qubist/typeO/gallery/prototype-curve.jpeg

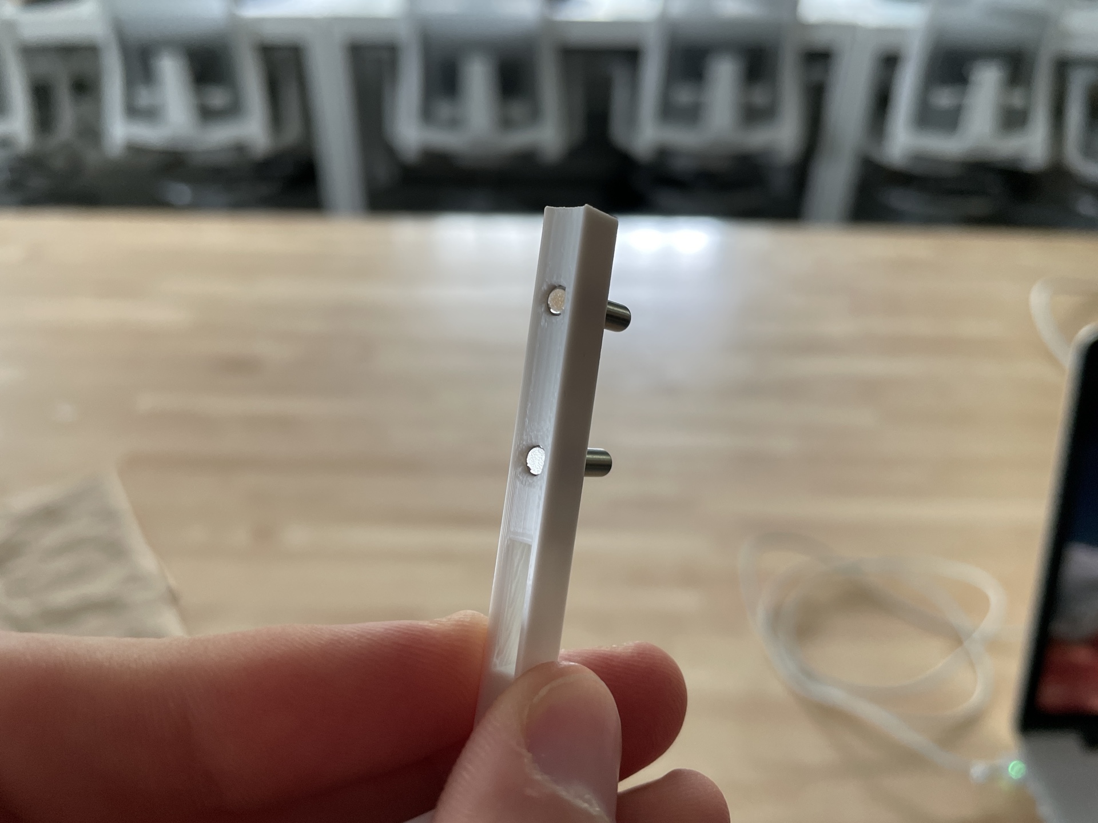
gallery/prototype-curve.jpeg
