qubist/typeO/gallery/prototype-lift.jpeg

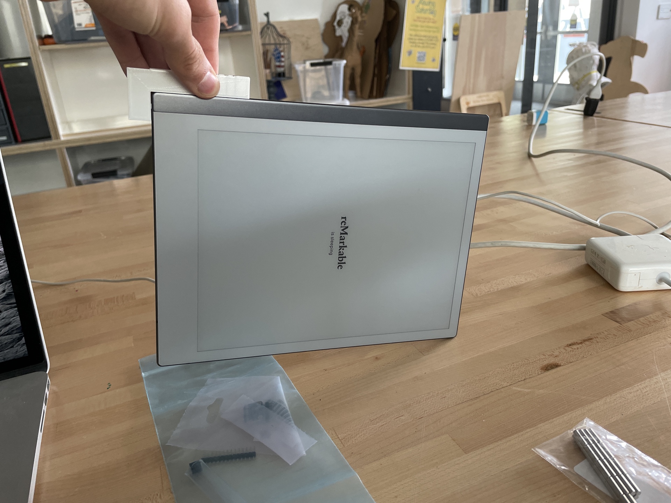
gallery/prototype-lift.jpeg
