qubist/typeO/gallery/magnet-measurements.jpeg

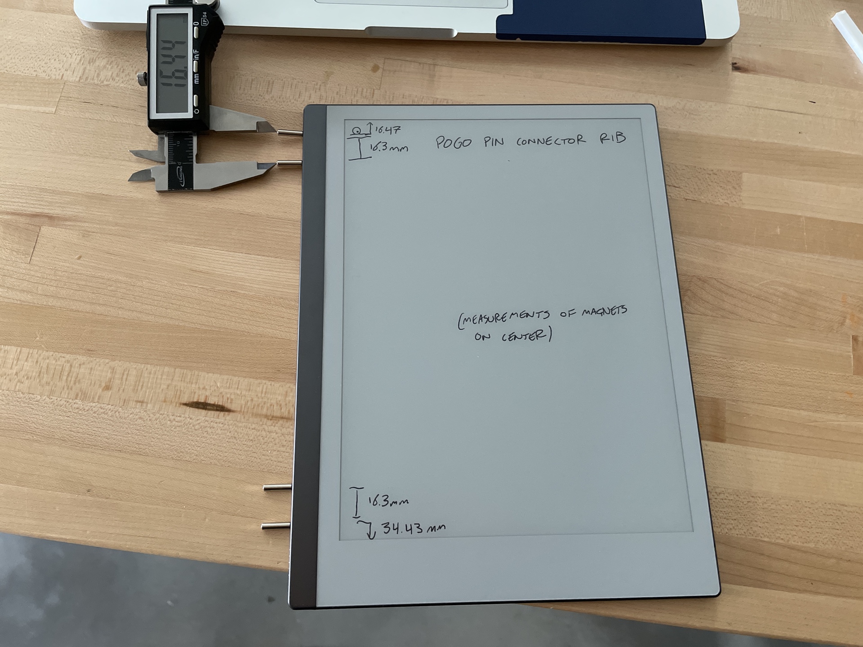
gallery/magnet-measurements.jpeg
